phenoptix/AVRISP/AVR ISP.sch

## KiCad design AVR ISP.sch (2013-09-02)

Schematic: AVR ISP.sch

Parts:
CON1: AVR-ISP-6
CON2: AVR-ISP-10
D1, D2, D3: LED
IC1: ATMEGA328-P; DIL28
IC2: ATTINY2313-P; DIP20
IC3: ATTINY85-S; SO8-200
IC4: ATTINY2313-S; SO20
R1, R2, R3: R
SHIELD1: ARDUINO_SHIELD

Notes on the sheet:
PROGRAMMING
ERROR
SLAVE RESET
HEARTBEAT
MOSI
MISO
SCK
